jeuxcing/theone/doc/mur.jpg

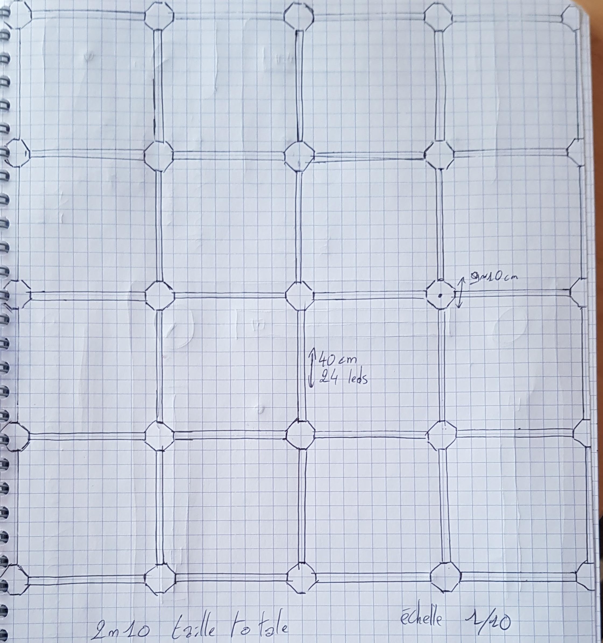
doc/mur.jpg
