jeuxcing/theone/doc/runner 3.jpg

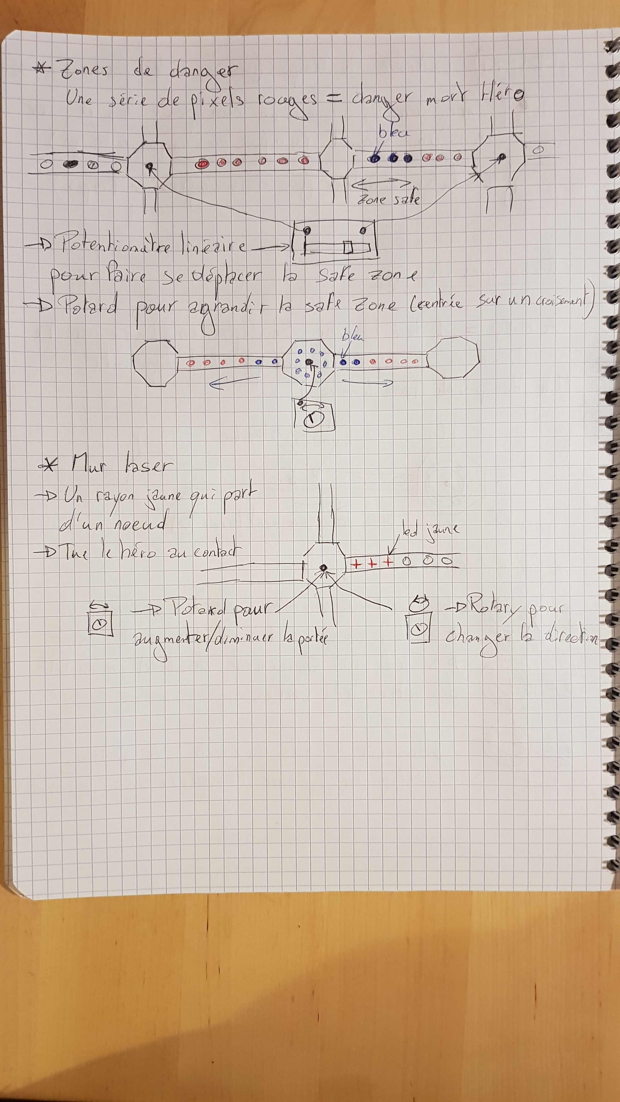
doc/runner 3.jpg
