jeuxcing/theone/doc/runner 4.jpg

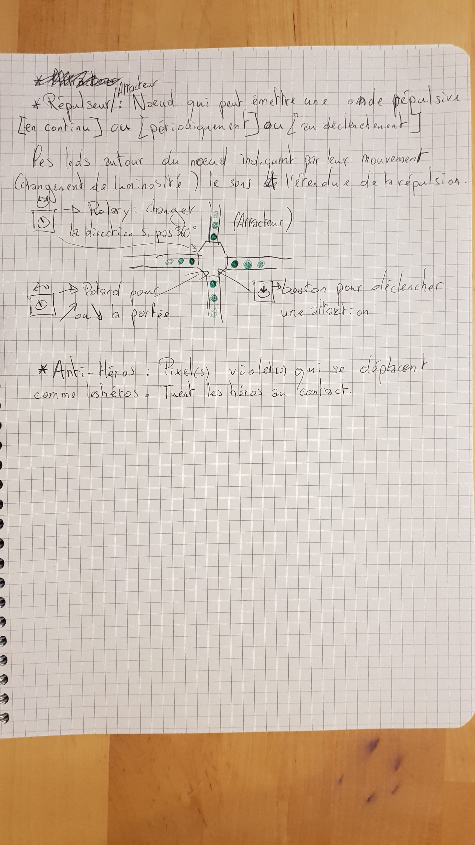
doc/runner 4.jpg
